TannerHollis/Lithium-Ion-Pack/Regulator_Enable_Simulation.asc

C2: cap; 1µ
D2: diode
D3: zener; 1N750
M1: nmos; Si7336ADP
M2: pmos; FDS4953
M3: nmos; Si7336ADP
M4: pmos; FDS4953
M5: nmos; Si7336ADP
R1: res; 10k
R2: res; 10k
R4: res; 10
R5: res; 10k
R6: res; 5
R7: res; 500k
V1: voltage; 18
V2: voltage; PULSE(0 5 10m 1u 1u 5m 10m)
V3: voltage; PULSE(0 5 20m 1u 1u 20m 40m)
V4: voltage; PULSE(0 3.3 10m 1u 1u 900m 1)
Named nets: 0
.tran 1s
