TannerHollis/Lithium-Ion-Pack/Op_Amp_Simulation.asc

C1: cap; 100n
C2: cap; 100n
I1: current; PULSE(0 0 5m 1n 1n 1 2 200)
R1: res; 0.002
R2: res; 165k
R3: res; 10
R4: res; 10
R5: res; 165k
R6: res; 13.8k
R7: res; 6k
R8: res; 5K
R9: res; 10k
R10: res; 10k
R11: res; 10k
R12: res; 10k
R13: res; 5k
R14: res; 5k
R15: res; 10k
R16: res; 10k
R17: res; 10k
R18: res; 10k
R19: res; 10k
R20: res; 10k
R21: res; 5k
R22: res; 5k
R23: res; 10k
R24: res; 10k
R25: res; 10k
R26: res; 10k
R27: res; 10k
R28: res; 10k
R29: res; 5k
R30: res; 5k
R31: res; 10k
R32: res; 10k
R33: res; 10k
R34: res; 10k
R35: res; 10k
R36: res; 10k
R37: res; 5k
R38: res; 5k
R39: res; 10k
R40: res; 10k
R41: res; 10k
R42: res; 10k
R43: res; 50
R44: res; 10k
R45: res; 5K
R46: res; 82.5K
R47: res; 82.5K
R48: res; 10k
R50: res; 0.05
R51: res; 0.002
U1: UniversalOpamp2
U2: UniversalOpamp2
U3: UniversalOpamp2
U4: UniversalOpamp2
U5: UniversalOpamp2
U6: UniversalOpamp2
U7: UniversalOpamp2
U8: UniversalOpamp2
U9: UniversalOpamp2
U10: UniversalOpamp2
U11: UniversalOpamp2
U12: UniversalOpamp2
V1: voltage; SINE(4.2 0 8)
V2: voltage; PULSE(16.8 16.9 0 1U 1U 0.5m 1m)
V3: voltage; 3.3v
V4: voltage; SINE(4.2 0 4)
V5: voltage; SINE(4.2 0 2)
V6: voltage; SINE(4.2 0 1)
V7: voltage; 3.3
Named nets: CSR+, CSR-, 1V65_Ref, 0, V_CSR, 3V3_Bus, 1V_Ref, V3, V2, V1, V4, V4-3, V4-3_Scaled, V3-2, V3-2_Scaled, V2-1, V2-1_Scaled, V1-GND, V1-GND_Scaled, CSR_CHG+, CSR_CHG-, V_CSR_CHG, Vopamp
.tran 50m
