TannerHollis/Lithium-Ion-Pack/Lithium_Ion_Pack/Connectors.sch

## KiCad design Lithium_Ion_Pack/Connectors.sch (2021-09-07)

Schematic: Connectors.sch

Parts:
D6: 3V3_LED; LED_1206_3216Metric_Pad1.42x1.75mm_HandSolder
D7: 5V_LED; LED_1206_3216Metric_Pad1.42x1.75mm_HandSolder
D8: CHG_LED; LED_1206_3216Metric_Pad1.42x1.75mm_HandSolder
H1, H2, H3, H4: MountingHole; MountingHole_2.5mm_Pad_TopBottom
J2: ON_SWITCH; PinHeader_1x02_P2.54mm_Vertical
J3: SWD; PinHeader_1x04_P2.54mm_Vertical
J4: UART; PinHeader_1x04_P2.54mm_Vertical
J5: GPIO; PinHeader_1x14_P2.54mm_Vertical
R57, R58, R59: 2K; R_1206_3216Metric_Pad1.30x1.75mm_HandSolder
S1: ON_SWITCH; SW_Push_1P1T_NO_CK_KMR2
TP2, TP3, TP4, TP5, TP6, TP7: TestPoint; Power_Tab
